lejoannac/blipyboard/production/firmware copy/kmk/quickpin/pro_micro/boardsource_blok.py

import board

pinout = [
    board.TX,
    board.RX,
    None,  # GND
    None,  # GND
    board.SDA,
    board.SCL,
    board.GP04,
    board.GP05,
    board.GP06,
    board.GP07,
    board.GP08,
    board.GP09,
    board.GP21,
    board.GP23,
    board.GP20,
    board.GP22,
    board.GP26,
    board.GP27,
    board.GP28,
    board.GP29,
    None,  # 3.3v
    None,  # RST
    None,  # GND
    None,  # RAW
]
