lejoannac/blipyboard/production/firmware copy/kmk/quickpin/pro_micro/nice_nano.py

import board

pinout = [
    board.TX,
    board.RX,
    None,  # GND
    None,  # GND
    board.SDA,
    board.SCL,
    board.P0_22,
    board.P0_24,
    board.P1_00,
    board.P0_11,
    board.P1_04,
    board.P1_06,
    board.P0_09,
    board.P0_10,
    board.P1_11,
    board.P1_13,
    board.P1_15,
    board.P0_02,
    board.P0_29,
    board.P0_31,
    None,  # 3.3v
    None,  # RST
    None,  # GND
    None,  # Battery+
]
